ivndbt/obiwanstenobit/docs/images/a03.jpg

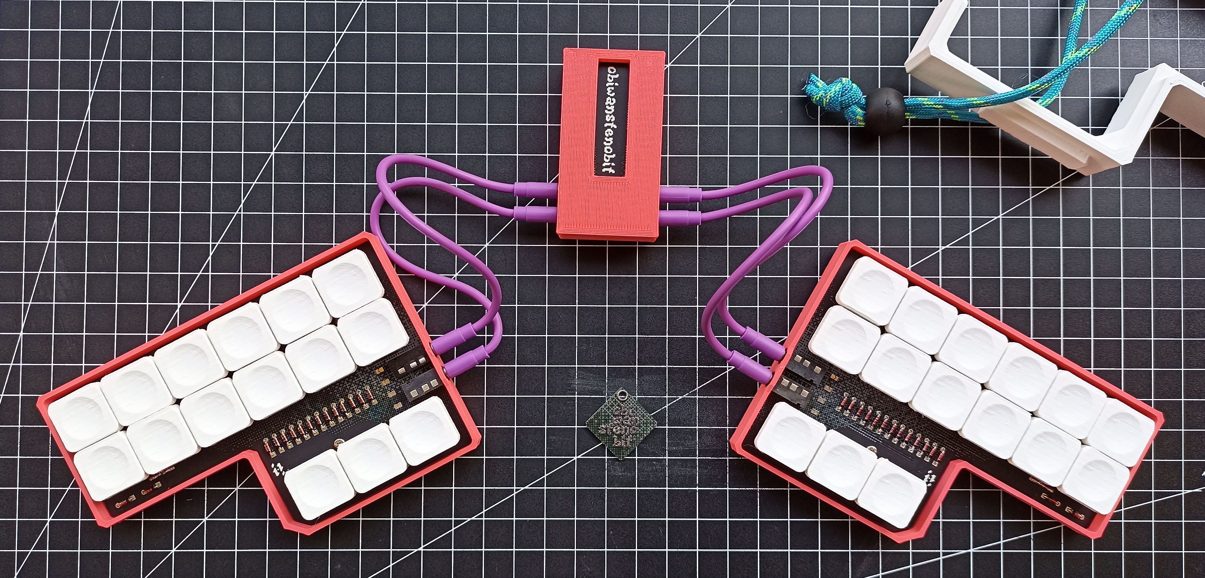
docs/images/a03.jpg
