ivndbt/obiwanstenobit/docs/images/a04.jpg

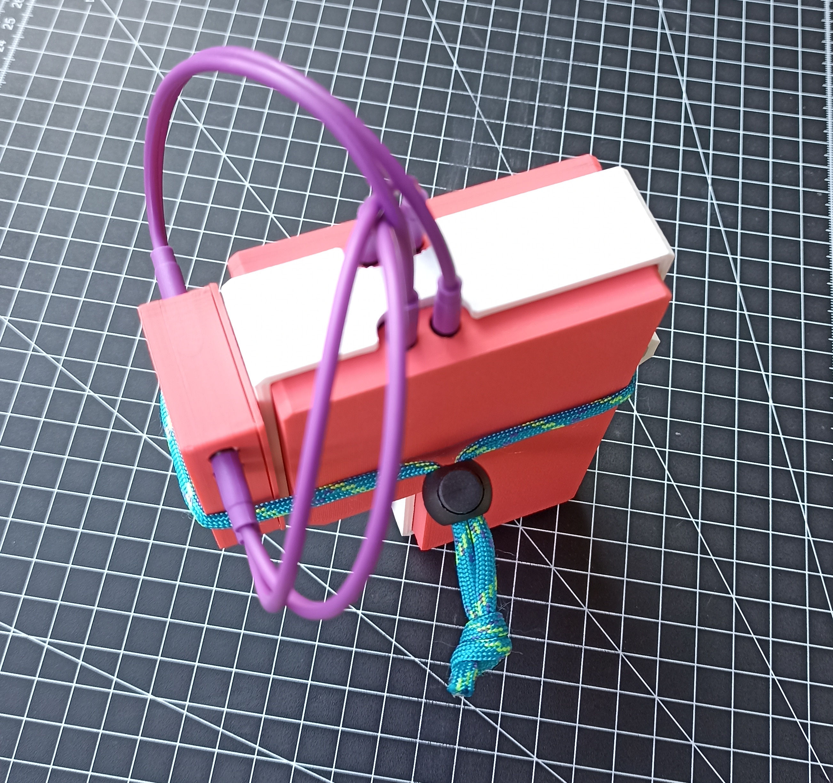
docs/images/a04.jpg
