ivndbt/obiwanstenobit/docs/images/b08a.jpg

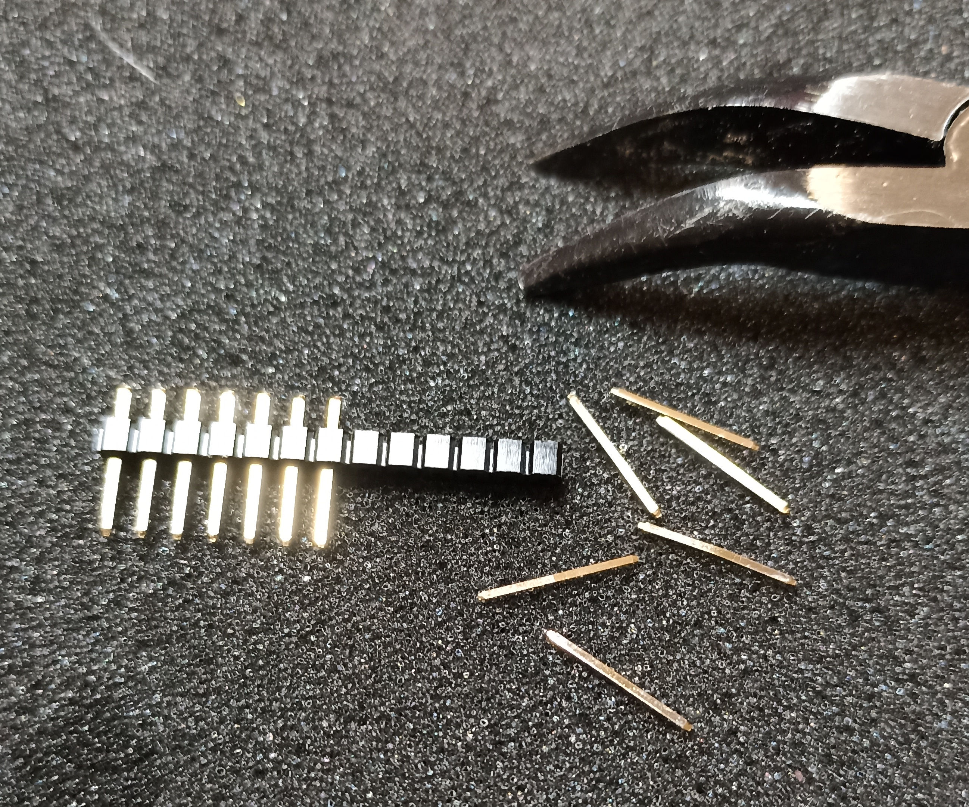
docs/images/b08a.jpg
