ivndbt/obiwanstenobit/hardware/pcb/kicad/obiwanstenobit.kicad_sch

## KiCad design hardware/pcb/kicad/obiwanstenobit.kicad_sch (2026-02-01)

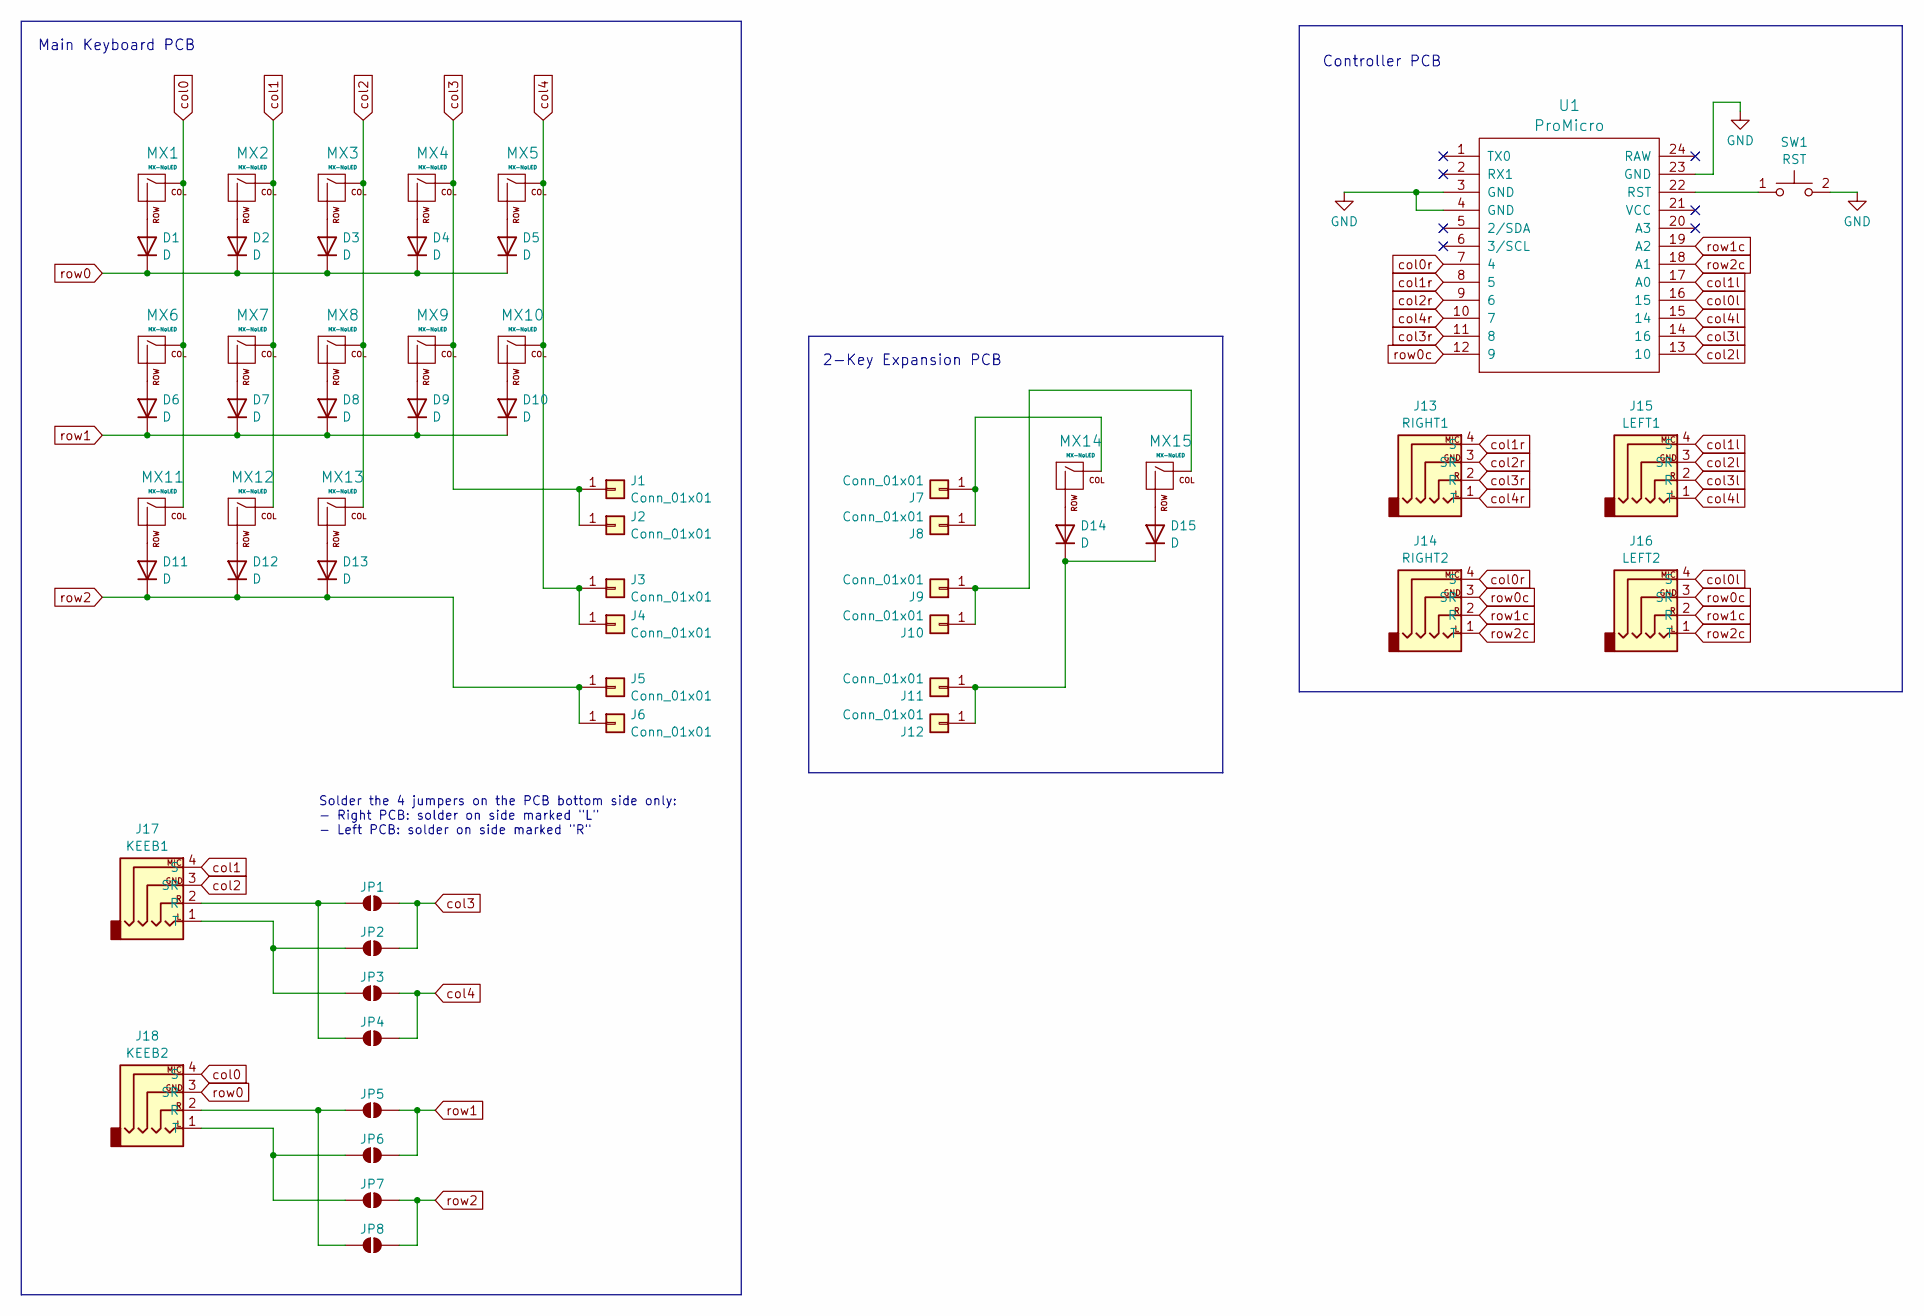
[picture p36: schematic obiwanstenobit.kicad_sch]

Parts:
D1, D2, D3, D4, D5, D6, D7, D8, D9, D10, D11, D12, D13, D14, D15: D; Diode_DO-35_SOD27_P5.08mm
J1, J2, J3, J4, J5, J6, J7, J8, J9, J10, J11, J12: Conn_01x01; Pad_SMD_Header_Lateral
J13: RIGHT1; TRRS-PJ-320A
J14: RIGHT2; TRRS-PJ-320A
J15: LEFT1; TRRS-PJ-320A
J16: LEFT2; TRRS-PJ-320A
J17: KEEB1; TRRS-PJ-320A-DoubleSided
J18: KEEB2; TRRS-PJ-320A-DoubleSided
JP1, JP2, JP3, JP4, JP5, JP6, JP7, JP8: SolderJumper_2_Open; SolderJumper-2_P1.3mm_Open_TrianglePad1.0x1.5mm
MX1, MX2, MX3, MX4, MX5, MX6, MX7, MX8, MX9, MX10, MX11, MX12, MX13, MX14, MX15: MX-NoLED; SW_Kailh_Choc_V1V2_1.00u-DoubleSided
SW1: RST; Button_SW_4x3mm_SMD
U1: ProMicro; ArduinoProMicro

Connections:
GND: SW1.2, U1.3 (GND), U1.4 (GND), U1.23 (GND)
unnamed: D1.2 (A), MX1.2 (ROW)
unnamed: D2.2 (A), MX2.2 (ROW)
unnamed: D3.2 (A), MX3.2 (ROW)
unnamed: D4.2 (A), MX4.2 (ROW)
unnamed: D5.2 (A), MX5.2 (ROW)
unnamed: D6.2 (A), MX6.2 (ROW)
unnamed: D7.2 (A), MX7.2 (ROW)
unnamed: D8.2 (A), MX8.2 (ROW)
unnamed: D9.2 (A), MX9.2 (ROW)
unnamed: D10.2 (A), MX10.2 (ROW)
unnamed: D11.2 (A), MX11.2 (ROW)
unnamed: D12.2 (A), MX12.2 (ROW)
unnamed: D13.2 (A), MX13.2 (ROW)
unnamed: D14.1 (K), D15.1 (K), J11.1, J12.1
unnamed: D14.2 (A), MX14.2 (ROW)
unnamed: D15.2 (A), MX15.2 (ROW)
unnamed: J7.1, J8.1, MX14.1 (COL)
unnamed: J9.1, J10.1, MX15.1 (COL)
unnamed: J17.1 (T), JP2.1 (A), JP3.1 (A)
unnamed: J17.2 (R), JP1.1 (A), JP4.1 (A)
unnamed: J18.1 (T), JP6.1 (A), JP7.1 (A)
unnamed: J18.2 (R), JP5.1 (A), JP8.1 (A)
unnamed: SW1.1, U1.22 (RST)
col0: J18.4 (S), MX1.1 (COL), MX6.1 (COL), MX11.1 (COL)
col0l: J16.4 (S), U1.16 (15)
col0r: J14.4 (S), U1.7 (4)
col1: J17.4 (S), MX2.1 (COL), MX7.1 (COL), MX12.1 (COL)
col1l: J15.4 (S), U1.17 (A0)
col1r: J13.4 (S), U1.8 (5)
col2: J17.3 (SR), MX3.1 (COL), MX8.1 (COL), MX13.1 (COL)
col2l: J15.3 (SR), U1.13 (10)
col2r: J13.3 (SR), U1.9 (6)
col3: J1.1, J2.1, JP1.2 (B), JP2.2 (B), MX4.1 (COL), MX9.1 (COL)
col3l: J15.2 (R), U1.14 (16)
col3r: J13.2 (R), U1.11 (8)
col4: J3.1, J4.1, JP3.2 (B), JP4.2 (B), MX5.1 (COL), MX10.1 (COL)
col4l: J15.1 (T), U1.15 (14)
col4r: J13.1 (T), U1.10 (7)
row0: D1.1 (K), D2.1 (K), D3.1 (K), D4.1 (K), D5.1 (K), J18.3 (SR)
row0c: J14.3 (SR), J16.3 (SR), U1.12 (9)
row1: D6.1 (K), D7.1 (K), D8.1 (K), D9.1 (K), D10.1 (K), JP5.2 (B), JP6.2 (B)
row1c: J14.2 (R), J16.2 (R), U1.19 (A2)
row2: D11.1 (K), D12.1 (K), D13.1 (K), J5.1, J6.1, JP7.2 (B), JP8.2 (B)
row2c: J14.1 (T), J16.1 (T), U1.18 (A1)

Notes on the sheet:
2-Key Expansion PCB
Main Keyboard PCB
Controller PCB
Solder the 4 jumpers on the PCB bottom side only: - Right PCB: solder on side marked "L" - Left PCB: solder on side marked "R"
